KROIA/Voicemail-Box/Software/BSP_VoiceMailBox/documentation/MP3_decoder.md

# MP3_decoder
The MP3 decoder library used in this project is from the [X-CUBE-AUDIO](https://www.st.com/en/embedded-software/x-cube-audio.html) example project.
The MP3_decoder class is just a C++ wrapper to make it easy to use the library.
The decoder is used to read mp3 encoded data from a source like a file and decode it back to audio samples that can then passed to the I2S TX DMA buffer, providing the speaker with sound.
You can find a ready to run project [here](../../Demos/F469/F469_MultiExample/README.md).

---
## Content
- [Features](#features)
- [Setup](#setup)
- [Usage](#usage)

---
## Features
- Decodes mp3 data live to analog samples

---
## Setup
- Uses the Spirit MP3 library for encoding and decoding. [Click here](../../Demos/F469/F469_HelloAudio/README.md/#spiritdsp-mp3) to learn how to include the library.
- Place a mp3 file with the name `music.mp3` onto the SD-Card.
- Make sure the C++ application is setup in order to use this class
You can find the instructions on how to do so [here](CppFromC.md).

---
## Usage
This example takes a `music.mp3` file and converts it to a `conv.wav` file.
``` C++ 
// Application.cpp
#include "BSP_VoiceMailBox.hpp" // includes "peripherals/i2s.hpp"

unsigned int decoderReadCallback(
        void* pMP3_decoderCompressedData,
        unsigned int nMP3_decoderDataSizeInChars,
        void* pUserData);

VoiceMailBox::WAVFile* wavFile = nullptr;
VoiceMailBox::File* mp3File = nullptr;
VoiceMailBox::MP3_decoder* decoder = nullptr;

void setup()
{
    // decoderReadCallback: function that gets called by the MP3_decoder to read compressed data from the MP3 file.
    // &mp3File: pointer to the MP3 file that is being read. (any void* can be used here, but we use a pointer to the MP3 file for convenience)
    // 4: samplesize in bytes. [int16_t(LEFT), int16_t(RIGHT)] is one sample
    decoder = new VoiceMailBox::MP3_decoder(decoderReadCallback, mp3File, 4);

    mp3File = new VoiceMailBox::File();
    wavFile = new VoiceMailBox::WAVFile();
    wavFile->setSampleRate(48000); // Set sample rate to 48kHz
    wavFile->setNumChannels(2);    // Stereo recording
    wavFile->setBitsPerSample(16); // Set bits per sample to 16

    if (!mp3File->open("music.mp3", VoiceMailBox::File::AccessMode::read))
    {
        VoiceMailBox::println("Failed to open file for reading.");
    }
    if (!wavFile->open("conv.wav", VoiceMailBox::File::AccessMode::write))
    {
        VoiceMailBox::println("Failed to open file for writing.");
    }
}

void loop()
{
    static bool finished = false;
    if (finished)
        return;
    if (!mp3File->isOpen())
    {
        VoiceMailBox::println("mp3File is not open");
        VoiceMailBox::delay(1000);
        return;
    }
    if (!wavFile->isOpen())
    {
        VoiceMailBox::println("wavFile is not open");
        VoiceMailBox::delay(1000);
        return;
    }

    const size_t sampleCount = 576; // Number of samples per frame for MP3 (2 channels, 16 bits per sample)
    int16_t data[sampleCount*2] = { 0 }; // Buffer to hold decoded audio samples
    VoiceMailBox::println("Starting MP3 decoding...");
    while (!mp3File->eof())
    {
        // Request <sampleCount> samples from the MP3 decoder
        unsigned int samplesRead = decoder->decode(data, sampleCount);
        static bool firstRun = true;
        if (firstRun)
        {
            samplesRead = decoder->decode(data, sampleCount); // For the first run, the decoding must be done twice to prevent noise
            firstRun = false;
        }
        if (samplesRead == 0)
        {
            // End of file
            break;
        }

        // Write the decoded audio data to the WAV file
        wavFile->writeAudioSamples(data, samplesRead); // 4 bytes per sample (2 channels * 2 bytes per channel)
    }
    VoiceMailBox::println("Decoding finished");
    mp3File->close();
    wavFile->close();
    finished = true;
}

// This function is called by the MP3_decoder to read compressed data from the MP3 file.
unsigned int decoderReadCallback(
    void* pMP3_decoderCompressedData,
    unsigned int nMP3_decoderDataSizeInChars,
    void* pUserData)
{
    // The pUserData is the pointer that was passed by the MP3_decoder constructor, which is a pointer to the mp3File->
    VoiceMailBox::File* file = (VoiceMailBox::File*)pUserData;
    if (file->isOpen())
    {
        // Read the MP3_decoder data from the file
        uint32_t bytesRead = file->read((uint8_t*)pMP3_decoderCompressedData, nMP3_decoderDataSizeInChars);
        return bytesRead;
    }
    return 0;
}
```
