KROIA/Voicemail-Box/Hardware/Diagramms/Blockschaltbild KW9.pdf

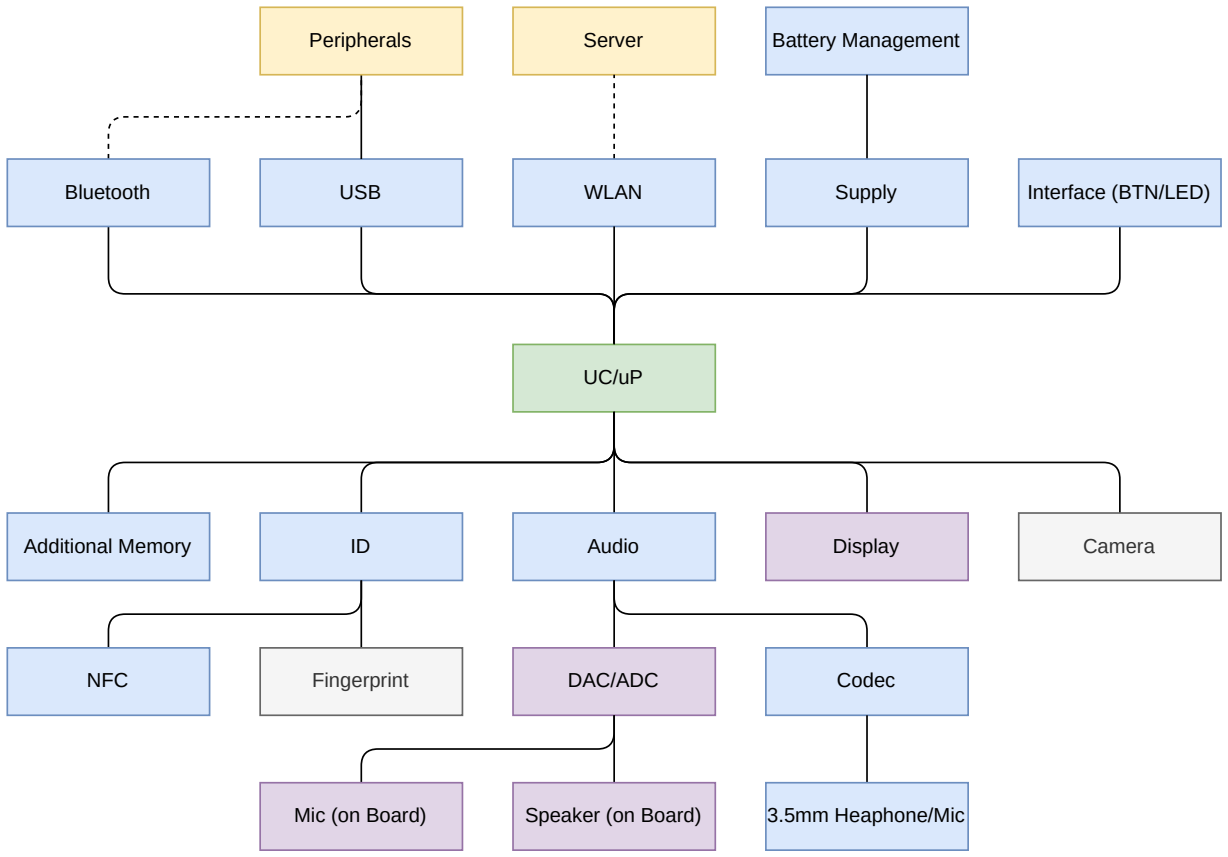
[picture p33: figure]
Bluetooth; USB; Peripherals; Server; WLAN; Battery Management; Supply; NFC; Fingerprint; Audio; DAC/ADC; Codec; Mic (on Board); Speaker (on Board); 3.5mm Heaphone/Mic; Display; Camera; Interface (BTN/LED); Additional Memory

Processor Source
Parts HW required
Parts HW Wish
Parts HW rejected
Parts external

Case
(3D Print)

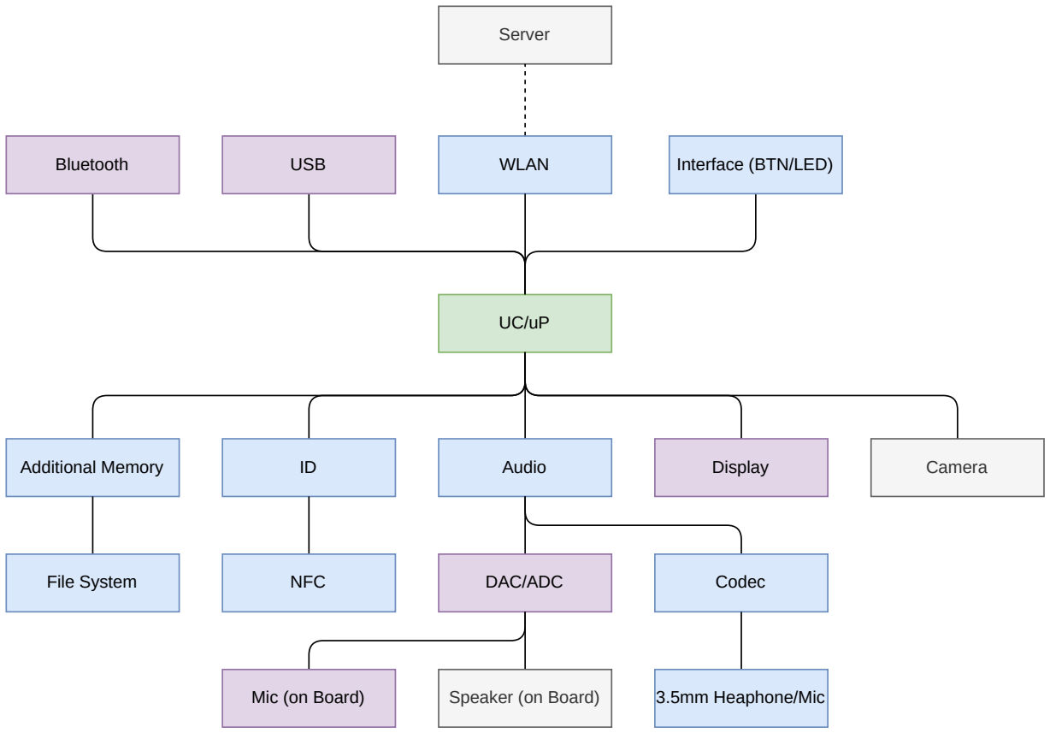
[picture p34: figure]
Bluetooth; USB; Server; WLAN; NFC; Audio; DAC/ADC; Codec; Mic (on Board); Speaker (on Board); 3.5mm Heaphone/Mic; Display; Camera; Interface (BTN/LED); Additional Memory; File System

Processor Source
SW required
SW Wish
SW if too much time
