KROIA/Voicemail-Box/Hardware/Picture/20250507_130045.jpg

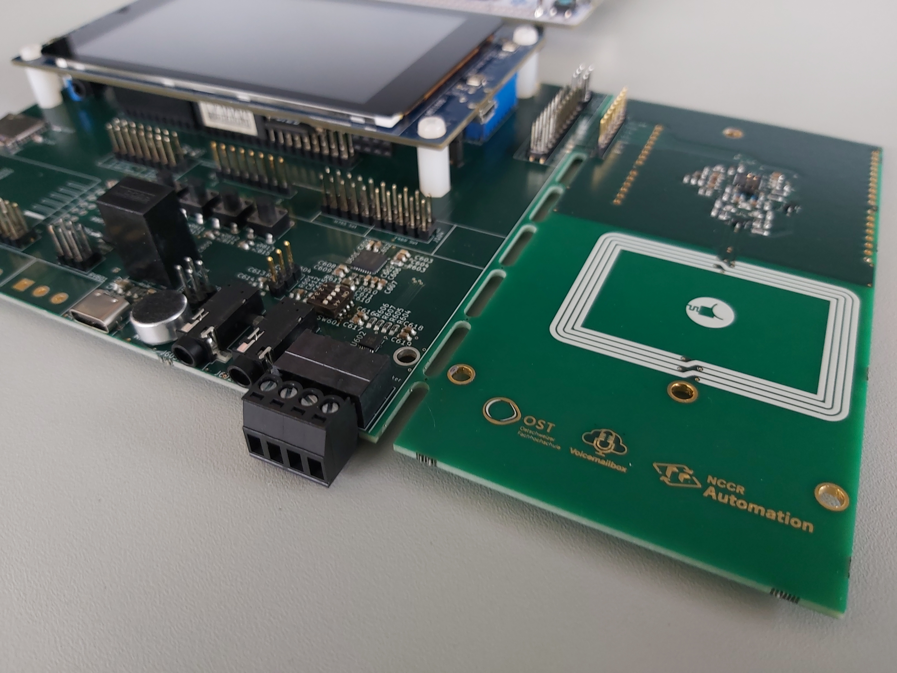
Hardware/Picture/20250507_130045.jpg
