KROIA/Voicemail-Box/Hardware/Picture/20250507_130126.jpg

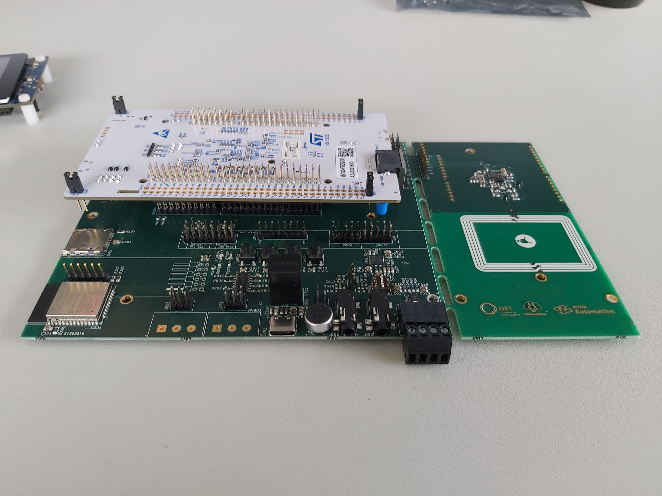
Hardware/Picture/20250507_130126.jpg
