KROIA/Voicemail-Box/Software/DevSandbox/Audio/Opus_bitrate+latency_comparison.svg.png

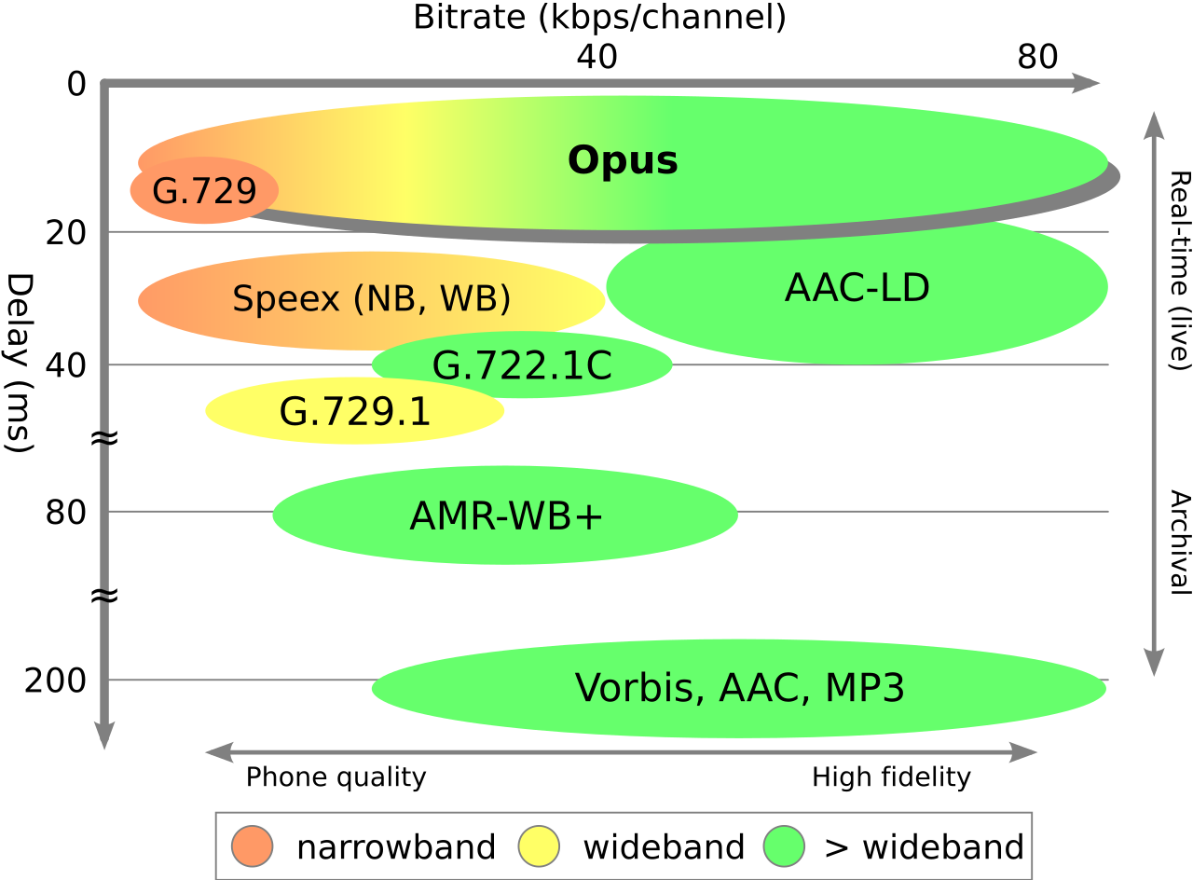
Software/DevSandbox/Audio/Opus_bitrate+latency_comparison.svg.png
