KROIA/Voicemail-Box/Software/BSP_VoiceMailBox/src/peripherals/Codec_TLV320AIC3104.cpp

#include "peripherals/Codec_TLV320AIC3104.hpp"
#include "platform.hpp"

namespace VoiceMailBox
{
	Codec_TLV320AIC3104::Codec_TLV320AIC3104(VMB_I2S_Handle* i2sHandle, uint16_t i2sBufferSize,
											 I2C& i2c, uint8_t i2cDeviceAddress,
											 VMB_GPIO* resetPort, uint16_t resetPin, bool resetPinIsInverted)
		: AudioCodec()
#ifdef VMB_USE_LOGGER_OBJECTS
		, Logger("Codec_TLV320AIC3104")
#endif
		, m_i2c(i2c)
		, m_i2cDeviceAddress(i2cDeviceAddress)
		, m_resetPin{ resetPort, resetPin, resetPinIsInverted }
		, m_i2s(i2sHandle, i2sBufferSize)
		, m_currentRegisterPage(0)
	{
#if defined(VMB_ENABLE_CODEC_PERFORMANCE_MEASUREMENTS)
		m_i2s.setHalfCpltCallback([this](I2S& caller) { onI2S_DMA_TxRx_HalfCpltCallback(); });
		m_i2s.setCpltCallback([this](I2S& caller) { onI2S_DMA_TxRx_CpltCallback(); });
#endif
	}

	Codec_TLV320AIC3104::~Codec_TLV320AIC3104()
	{

	}

	void Codec_TLV320AIC3104::reset()
	{
		m_resetPin.set(true); 
		VMB_HAL_Delay(25); // Wait for 10ms
		m_resetPin.set(false); 
		VMB_HAL_Delay(25); // Wait for 10ms

		// Software reset
		writeRegister(REG::PAGE_0::SOFTWRE_RESET, 0x01); // Example register write for software reset
		VMB_HAL_Delay(10); // Wait for 10ms
	}
	bool Codec_TLV320AIC3104::setup()
	{
		bool success = true;
		reset(); // Reset the codec
		setCurrentRegisterPage(0); // Set the current register page to 0

		// Initialize codec registers
		success &= writeRegister(REG::PAGE_0::PLL_PROGRAMMING_A, 0x10); //Disable PLL, 2 = 4. MCLK = 256 * 48Khz, fs(ref) = MCLK / (128 * Q)


		float gainDB = 0;
		uint32_t microphoneGainDB_2 = (uint32_t)(2.f * gainDB) & 0xEF;
		success &= writeRegister(REG::PAGE_0::LEFT_ADC_PGA_GAIN_CONTROL,  0x00 | microphoneGainDB_2); //Un-mute left ADC PGA
		success &= writeRegister(REG::PAGE_0::RIGHT_ADC_PGA_GAIN_CONTROL, 0x00 | microphoneGainDB_2); //Un-mute right ADC PGA
		success &= writeRegister(REG::PAGE_0::MIC2_L_R_TO_LEFT_ADC_CONTROL, 0x0F); //Connect MIC2L/LINE2L to left ADC PGA (@0db gain), do not connect MIC2R/LINE2R to left ADC PGA
		success &= writeRegister(REG::PAGE_0::MIC2_LINE2_TO_RIGHT_ADC_CONTROL, 0xF0); //Connect MIC2R/LINE2R to right ADC PGA (@0db gain), do not connect MIC2L/LINE2L to right ADC PGA
		success &= writeRegister(REG::PAGE_0::MIC1LP_LINE1LP_TO_LEFT_ADC_CONTROL, 0x7C); //Power up left ADC
		success &= writeRegister(REG::PAGE_0::MIC1RP_LINE1RP_TO_RIGHT_ADC_CONTROL, 0x7C); //Power up right ADC


		success &= writeRegister(REG::PAGE_0::CODEC_DATA_PATH_SETUP, 0x0A); //fs(ref) = 48khz, left DAC data path plays left-channel input data, right DAC -> right-channel input data

		
		

		success &= writeRegister(REG::PAGE_0::AUDIO_SERIAL_DATA_INTERFACE_CONTROL_B, 0x07); // Enable Re-Sync for ADC and DAC

		success &= writeRegister(REG::PAGE_0::AUDIO_CODEC_DIGITAL_FILTER_CONTROL, 0x00); // Bypass digital filter
		success &= writeRegister(REG::PAGE_0::AUDIO_SERIAL_DATA_INTERFACE_CONTROL_A, 0x00); // Disable 3D effect and others
		

		success &= writeRegister(REG::PAGE_0::DAC_OUTPUT_SWITCHING_CONTROL, 0xA0); // Set Output-switch of DAC_L -> DAC_L2, DAC_R -> DAC_R2


		success &= writeRegister(REG::PAGE_0::DAC_L1_TO_HPLOUT_VOLUME_CONTROL, 0x00); // Disconnect DAC_L1 from HPLOUT
		success &= writeRegister(REG::PAGE_0::DAC_R1_TO_HPLOUT_VOLUME_CONTROL, 0x00); // Disconnect DAC_R1 from HPLOUT
		success &= writeRegister(REG::PAGE_0::PGA_L_TO_HPLOUT_VOLUME_CONTROL, 0x00); // Disconnect PGA_L from HPLOUT
		success &= writeRegister(REG::PAGE_0::PGA_R_TO_HPLOUT_VOLUME_CONTROL, 0x00); // Disconnect PGA_R from HPLOUT

		success &= writeRegister(REG::PAGE_0::DAC_L1_TO_HPROUT_VOLUME_CONTROL, 0x00); // Disconnect DAC_L1 from HPROUT
		success &= writeRegister(REG::PAGE_0::DAC_R1_TO_HPROUT_VOLUME_CONTROL, 0x00); // Disconnect DAC_R1 from HPROUT
		success &= writeRegister(REG::PAGE_0::PGA_L_TO_HPROUT_VOLUME_CONTROL, 0x00); // Disconnect PGA_L from HPROUT
		success &= writeRegister(REG::PAGE_0::PGA_R_TO_HPROUT_VOLUME_CONTROL, 0x00); // Disconnect PGA_R from HPROUT

		

		success &= writeRegister(REG::PAGE_0::LEFT_DAC_DIGITAL_VOLUME_CONTROL, 0x00); //Unmute left DAC channel
		success &= writeRegister(REG::PAGE_0::RIGHT_DAC_DIGITAL_VOLUME_CONTROL, 0x00); //Unmute right DAC channel
		success &= writeRegister(REG::PAGE_0::HPLOUT_OUTPUT_LEVEL_CONTROL, 0x0B); //Unmute left line output (HPLOUT) @ 0dB gain
		success &= writeRegister(REG::PAGE_0::HPROUT_OUTPUT_LEVEL_CONTROL, 0x0B); //Unmute right line output (HPROUT) @ 0dB gain


		success &= writeRegister(REG::PAGE_0::ADC_POWER_AND_OUTPUT_DRIVER_CONTROL, 0xA0); //Power up left and right DAC



		//writeRegister(REG::PAGE_0::HIGH_POWER_OUTPUT_STAGE_CONTROL, 0x80); //Output common mode voltage = 1,65V (= VCC / 2)
		
		//writeRegister(REG::PAGE_0::DAC_L1_TO_LEFT_LOP_M_VOLUME_CONTROL, 0x80); //Route left DAC to left line output
		//writeRegister(REG::PAGE_0::LEFT_LOP_M_OUTPUT_LEVEL_CONTROL, 0x0B); //Unmute left line output
		success &= writeRegister(REG::PAGE_0::CLOCK, 0x01); //CODEC_CLKIN uses CLKDIV_OUT

		// Setup I2S for DMA transmit and receive
		if (!m_i2s.startDMA())
		{
			VMB_LOGLN("Failed to start I2S DMA");
			success = false;
		}
		if (!success)
		{
			VMB_LOGLN("Codec_TLV320AIC3104 setup failed");
		}
		return success;
	}

	void Codec_TLV320AIC3104::onI2S_DMA_TxRx_HalfCpltCallback()
	{
		// Inside ISR context! 
#ifdef VMB_ENABLE_CODEC_PERFORMANCE_MEASUREMENTS
		m_DMA_halfTransferTick = VMB_HAL_GetTickCountInMs();
#endif
#if  defined(VMB_DEVELOPMENT_ENABLE_DBG_PINS_IN_CODEC) && defined(VMB_USE_INTERNAL_LEDS)
		Platform::getDebugPin(DBG_PIN::DBG0).set(1); // Set DBG0 on
#endif
	}
	void Codec_TLV320AIC3104::onI2S_DMA_TxRx_CpltCallback()
	{
		// Inside ISR context! 
#ifdef VMB_ENABLE_CODEC_PERFORMANCE_MEASUREMENTS
		m_DMA_halfProcessingTicks = VMB_HAL_GetTickCountInMs() - m_DMA_halfTransferTick;
#endif
#if defined(VMB_DEVELOPMENT_ENABLE_DBG_PINS_IN_CODEC) && defined(VMB_USE_INTERNAL_LEDS)
		Platform::getDebugPin(DBG_PIN::DBG0).set(0); // Set DBG0 off
#endif
	}


	void Codec_TLV320AIC3104::startDataProcessing()
	{
#ifdef VMB_ENABLE_CODEC_PERFORMANCE_MEASUREMENTS
		m_startDataProcessingTick = VMB_HAL_GetTickCountInMs();
#endif
	}
	void Codec_TLV320AIC3104::endDataProcessing()
	{
#ifdef VMB_ENABLE_CODEC_PERFORMANCE_MEASUREMENTS
		m_dataProcessingTicks = VMB_HAL_GetTickCountInMs() - m_startDataProcessingTick;
#endif
	}

	void Codec_TLV320AIC3104::setMicrophoneGainDB(float db)
	{
		uint8_t leftGainReg = readRegister(REG::PAGE_0::LEFT_ADC_PGA_GAIN_CONTROL);
		uint8_t rightGainReg = readRegister(REG::PAGE_0::RIGHT_ADC_PGA_GAIN_CONTROL);

		if(db < 0)
			db = 0;
		else if (db > 59.5)
			db = 59.5;
		uint32_t microphoneGainDB_2 = (uint32_t)(2.f * db) & 0xEF;
		leftGainReg  = (leftGainReg & 0x01)  | microphoneGainDB_2;
		rightGainReg = (rightGainReg & 0x01) | microphoneGainDB_2;

		writeRegister(REG::PAGE_0::LEFT_ADC_PGA_GAIN_CONTROL, leftGainReg); //Un-mute left ADC PGA
		writeRegister(REG::PAGE_0::RIGHT_ADC_PGA_GAIN_CONTROL, rightGainReg); //Un-mute right ADC PGA
	}

	bool Codec_TLV320AIC3104::writeRegister(uint8_t registerAddress, uint8_t data)
	{
		VMB_HAL_Status status = m_i2c.writeRegister(m_i2cDeviceAddress, registerAddress, data);
		VMB_LOGGER_LOG_STATUS(status, "Codec_TLV320AIC3104::writeRegister("+std::to_string(registerAddress)+","+std::to_string(data)+")");
		return status == VMB_HAL_Status::OK;
	}

	uint8_t Codec_TLV320AIC3104::readRegister(uint8_t registerAddress)
	{
		uint8_t data = 0;
		VMB_HAL_Status status = m_i2c.readRegister(m_i2cDeviceAddress, registerAddress, data);
		VMB_LOGGER_LOG_STATUS(status, "Codec_TLV320AIC3104::readRegister("+std::to_string(registerAddress)+")");
		return data;
	}

	uint8_t Codec_TLV320AIC3104::getCurrentRegisterPage()
	{
		return readRegister(REG::PAGE_0::PAGE_SELECT); // Read the current register page
	}
	void Codec_TLV320AIC3104::setCurrentRegisterPage(uint8_t page)
	{
		writeRegister(REG::PAGE_0::PAGE_SELECT, page & 0x01); // Set the current register page
		m_currentRegisterPage = page & 0x01; // Update the current register page

		// Readback the current register page to verify
		uint8_t currentPage = getCurrentRegisterPage();
		if (currentPage != m_currentRegisterPage)
		{
			// Handle error
			VMB_LOGLN("Failed to set register page to " + std::to_string(page) + ", current page is " + std::to_string(currentPage));
		}
	}


	
}
