KROIA/Voicemail-Box/Software/Demos/F469/F469_HelloAudio/Core/Src/main.c

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
/* Includes ------------------------------------------------------------------*/
#include "main.h"
#include "fatfs.h"
#include "usb_host.h"

/* USER CODE BEGIN Includes */
#include "Application.h"
/* USER CODE END Includes */

ADC_HandleTypeDef hadc1;
ADC_HandleTypeDef hadc2;

CRC_HandleTypeDef hcrc;

DMA2D_HandleTypeDef hdma2d;

DSI_HandleTypeDef hdsi;

I2C_HandleTypeDef hi2c1;
I2C_HandleTypeDef hi2c2;

I2S_HandleTypeDef hi2s2;
DMA_HandleTypeDef hdma_i2s2_ext_rx;
DMA_HandleTypeDef hdma_spi2_tx;

LTDC_HandleTypeDef hltdc;

SD_HandleTypeDef hsd;
DMA_HandleTypeDef hdma_sdio_rx;
DMA_HandleTypeDef hdma_sdio_tx;

TIM_HandleTypeDef htim1;

UART_HandleTypeDef huart3;
UART_HandleTypeDef huart6;

SDRAM_HandleTypeDef hsdram1;

/* USER CODE BEGIN PV */
ADC_HandleTypeDef* getADC_POT0()
{
	return &hadc1;
}
ADC_HandleTypeDef* getADC_POT1()
{
	return &hadc2;
}
UART_HandleTypeDef* getUART_DEBUG()
{
	return &huart3;
}
UART_HandleTypeDef* getUART_WIFI()
{
	return &huart6;
}
I2C_HandleTypeDef* getI2C_Handle()
{
	return &hi2c1;
}
I2S_HandleTypeDef* getI2S_CODEC()
{
	return &hi2s2;
}
/* USER CODE END PV */

void SystemClock_Config(void);
void PeriphCommonClock_Config(void);
static void MX_GPIO_Init(void);
static void MX_DMA_Init(void);
static void MX_CRC_Init(void);
static void MX_DMA2D_Init(void);
static void MX_DSIHOST_DSI_Init(void);
static void MX_FMC_Init(void);
static void MX_I2C1_Init(void);
static void MX_I2C2_Init(void);
static void MX_LTDC_Init(void);
static void MX_SDIO_SD_Init(void);
static void MX_TIM1_Init(void);
static void MX_USART3_UART_Init(void);
static void MX_USART6_UART_Init(void);
static void MX_ADC1_Init(void);
static void MX_ADC2_Init(void);
static void MX_I2S2_Init(void);
void MX_USB_HOST_Process(void);

/**
  * @brief  The application entry point.
  * @retval int
  */
int main(void)
{

  /* MCU Configuration--------------------------------------------------------*/

  /* Reset of all peripherals, Initializes the Flash interface and the Systick. */
  HAL_Init();

  /* Configure the system clock */
  SystemClock_Config();

  /* Configure the peripherals common clocks */
  PeriphCommonClock_Config();

  /* Initialize all configured peripherals */
  MX_GPIO_Init();
  MX_DMA_Init();
  MX_CRC_Init();
  MX_DMA2D_Init();
  MX_DSIHOST_DSI_Init();
  MX_FMC_Init();
  MX_I2C1_Init();
  MX_I2C2_Init();
  MX_LTDC_Init();
  MX_SDIO_SD_Init();
  MX_TIM1_Init();
  MX_USART3_UART_Init();
  MX_USART6_UART_Init();
  MX_FATFS_Init();
  MX_USB_HOST_Init();
  MX_ADC1_Init();
  MX_ADC2_Init();
  MX_I2S2_Init();
  /* USER CODE BEGIN 2 */
  setup(); // Calls the setup function from the Application.h
  /* USER CODE END 2 */

  /* Infinite loop */
  /* USER CODE BEGIN WHILE */
  while (1)
  {
	loop(); // Calls the loop function from the Application.h
    /* USER CODE END WHILE */
    MX_USB_HOST_Process();

    /* USER CODE BEGIN 3 */
  }
  /* USER CODE END 3 */
}

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
/**
  * @brief  Period elapsed callback in non blocking mode
  * @note   This function is called  when TIM6 interrupt took place, inside
  * HAL_TIM_IRQHandler(). It makes a direct call to HAL_IncTick() to increment
  * a global variable "uwTick" used as application time base.
  * @param  htim : TIM handle
  * @retval None
  */
void HAL_TIM_PeriodElapsedCallback(TIM_HandleTypeDef *htim)
{
  if (htim->Instance == TIM6) {
    HAL_IncTick();
  }
}

/**
  * @brief  This function is executed in case of error occurrence.
  * @retval None
  */
void Error_Handler(void)
{
  /* USER CODE BEGIN Error_Handler_Debug */
  /* User can add his own implementation to report the HAL error return state */
  __disable_irq();
  while (1)
  {
  }
  /* USER CODE END Error_Handler_Debug */
}

#ifdef  USE_FULL_ASSERT
/**
  * @brief  Reports the name of the source file and the source line number
  *         where the assert_param error has occurred.
  * @param  file: pointer to the source file name
  * @param  line: assert_param error line source number
  * @retval None
  */
void assert_failed(uint8_t *file, uint32_t line)
{
  /* USER CODE BEGIN 6 */
  /* User can add his own implementation to report the file name and line number,
     ex: printf("Wrong parameters value: file %s on line %d\r\n", file, line) */
  /* USER CODE END 6 */
}
#endif /* USE_FULL_ASSERT */
