KROIA/Voicemail-Box/Software/Demos/H755/H755_HelloAudio/CM7/Core/Src/main.c

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
/* Includes ------------------------------------------------------------------*/
#include "main.h"
#include "fatfs.h"

/* USER CODE BEGIN Includes */
#include "Application.h"
/* USER CODE END Includes */

/* USER CODE BEGIN PD */

#ifndef HSEM_ID_0
#define HSEM_ID_0 (0U) /* HW semaphore 0*/
#endif

/* USER CODE END PD */

ADC_HandleTypeDef hadc1;
ADC_HandleTypeDef hadc3;

I2C_HandleTypeDef hi2c1;

I2S_HandleTypeDef hi2s2;

SD_HandleTypeDef hsd1;

UART_HandleTypeDef huart1;
UART_HandleTypeDef huart3;

/* USER CODE BEGIN PV */
ADC_HandleTypeDef* getADC_POT0()
{
	return &hadc1;
}
ADC_HandleTypeDef* getADC_POT1()
{
	return &hadc3;
}
UART_HandleTypeDef* getUART_DEBUG()
{
	return &huart3;
}
UART_HandleTypeDef* getUART_WIFI()
{
	return &huart1;
}
I2C_HandleTypeDef* getI2C_Handle()
{
	return &hi2c1;
}
I2S_HandleTypeDef* getI2S_CODEC()
{
	return &hi2s2;
}
/* USER CODE END PV */

void SystemClock_Config(void);
void PeriphCommonClock_Config(void);
static void MX_GPIO_Init(void);
static void MX_ADC1_Init(void);
static void MX_ADC3_Init(void);
static void MX_USART1_UART_Init(void);
static void MX_USART3_UART_Init(void);
static void MX_I2C1_Init(void);
static void MX_SDMMC1_SD_Init(void);
static void MX_I2S2_Init(void);
/**
  * @brief  The application entry point.
  * @retval int
  */
int main(void)
{

/* USER CODE BEGIN Boot_Mode_Sequence_0 */
  int32_t timeout;
/* USER CODE END Boot_Mode_Sequence_0 */

/* USER CODE BEGIN Boot_Mode_Sequence_1 */
  /* Wait until CPU2 boots and enters in stop mode or timeout*/
  timeout = 0xFFFF;
  while((__HAL_RCC_GET_FLAG(RCC_FLAG_D2CKRDY) != RESET) && (timeout-- > 0));
  if ( timeout < 0 )
  {
  Error_Handler();
  }
/* USER CODE END Boot_Mode_Sequence_1 */
  /* MCU Configuration--------------------------------------------------------*/

  /* Reset of all peripherals, Initializes the Flash interface and the Systick. */
  HAL_Init();

  /* Configure the system clock */
  SystemClock_Config();

  /* Configure the peripherals common clocks */
  PeriphCommonClock_Config();
/* USER CODE BEGIN Boot_Mode_Sequence_2 */
/* When system initialization is finished, Cortex-M7 will release Cortex-M4 by means of
HSEM notification */
/*HW semaphore Clock enable*/
__HAL_RCC_HSEM_CLK_ENABLE();
/*Take HSEM */
HAL_HSEM_FastTake(HSEM_ID_0);
/*Release HSEM in order to notify the CPU2(CM4)*/
HAL_HSEM_Release(HSEM_ID_0,0);
/* wait until CPU2 wakes up from stop mode */
timeout = 0xFFFF;
while((__HAL_RCC_GET_FLAG(RCC_FLAG_D2CKRDY) == RESET) && (timeout-- > 0));
if ( timeout < 0 )
{
Error_Handler();
}
/* USER CODE END Boot_Mode_Sequence_2 */

  /* Initialize all configured peripherals */
  MX_GPIO_Init();
  MX_ADC1_Init();
  MX_ADC3_Init();
  MX_USART1_UART_Init();
  MX_USART3_UART_Init();
  MX_I2C1_Init();
  MX_FATFS_Init();
  MX_SDMMC1_SD_Init();
  MX_I2S2_Init();
  /* Infinite loop */
  /* USER CODE BEGIN WHILE */
  setup();
  while (1)
  {

	  loop();
    /* USER CODE END WHILE */

    /* USER CODE BEGIN 3 */
  }
  /* USER CODE END 3 */
}

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
