KROIA/Voicemail-Box/Software/DevSandbox/NFC/NFC_Demo/CM7/Core/Inc/custom_bus.h

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

/* Define to prevent recursive inclusion -------------------------------------*/
#ifndef CUSTOM_BUS_H
#define CUSTOM_BUS_H

#ifdef __cplusplus
 extern "C" {
#endif

/* Includes ------------------------------------------------------------------*/
#include "custom_conf.h"
#include "custom_errno.h"

/** @addtogroup BSP
  * @{
  */

/** @addtogroup CUSTOM
  * @{
  */

/** @defgroup CUSTOM_BUS CUSTOM BUS
  * @{
  */

/** @defgroup CUSTOM_BUS_Exported_Constants CUSTOM BUS Exported Constants
  * @{
  */

#define BUS_SPI1_INSTANCE SPI1
#define BUS_SPI1_SCK_GPIO_CLK_DISABLE() __HAL_RCC_GPIOA_CLK_DISABLE()
#define BUS_SPI1_SCK_GPIO_PORT GPIOA
#define BUS_SPI1_SCK_GPIO_PIN GPIO_PIN_5
#define BUS_SPI1_SCK_GPIO_AF GPIO_AF5_SPI1
#define BUS_SPI1_SCK_GPIO_CLK_ENABLE() __HAL_RCC_GPIOA_CLK_ENABLE()
#define BUS_SPI1_MISO_GPIO_PIN GPIO_PIN_6
#define BUS_SPI1_MISO_GPIO_PORT GPIOA
#define BUS_SPI1_MISO_GPIO_CLK_DISABLE() __HAL_RCC_GPIOA_CLK_DISABLE()
#define BUS_SPI1_MISO_GPIO_CLK_ENABLE() __HAL_RCC_GPIOA_CLK_ENABLE()
#define BUS_SPI1_MISO_GPIO_AF GPIO_AF5_SPI1
#define BUS_SPI1_MOSI_GPIO_CLK_ENABLE() __HAL_RCC_GPIOB_CLK_ENABLE()
#define BUS_SPI1_MOSI_GPIO_PORT GPIOB
#define BUS_SPI1_MOSI_GPIO_PIN GPIO_PIN_5
#define BUS_SPI1_MOSI_GPIO_CLK_DISABLE() __HAL_RCC_GPIOB_CLK_DISABLE()
#define BUS_SPI1_MOSI_GPIO_AF GPIO_AF5_SPI1

#ifndef BUS_SPI1_POLL_TIMEOUT
  #define BUS_SPI1_POLL_TIMEOUT                   0x1000U
#endif
/* SPI1 Baud rate in bps  */
#ifndef BUS_SPI1_BAUDRATE
   #define BUS_SPI1_BAUDRATE   10000000U /* baud rate of SPIn = 10 Mbps*/
#endif

/**
  * @}
  */

/** @defgroup CUSTOM_BUS_Private_Types CUSTOM BUS Private types
  * @{
  */
#if (USE_HAL_SPI_REGISTER_CALLBACKS == 1U)
typedef struct
{
  pSPI_CallbackTypeDef  pMspInitCb;
  pSPI_CallbackTypeDef  pMspDeInitCb;
}BSP_SPI_Cb_t;
#endif /* (USE_HAL_SPI_REGISTER_CALLBACKS == 1U) */
/**
  * @}
  */

/** @defgroup CUSTOM_LOW_LEVEL_Exported_Variables LOW LEVEL Exported Constants
  * @{
  */

extern SPI_HandleTypeDef hspi1;

/**
  * @}
  */

/** @addtogroup CUSTOM_BUS_Exported_Functions
  * @{
  */

/* BUS IO driver over SPI Peripheral */
HAL_StatusTypeDef MX_SPI1_Init(SPI_HandleTypeDef* hspi);
int32_t BSP_SPI1_Init(void);
int32_t BSP_SPI1_DeInit(void);
int32_t BSP_SPI1_Send(uint8_t *pData, uint16_t Length);
int32_t BSP_SPI1_Recv(uint8_t *pData, uint16_t Length);
int32_t BSP_SPI1_SendRecv(uint8_t *pTxData, uint8_t *pRxData, uint16_t Length);
#if (USE_HAL_SPI_REGISTER_CALLBACKS == 1U)
int32_t BSP_SPI1_RegisterDefaultMspCallbacks (void);
int32_t BSP_SPI1_RegisterMspCallbacks (BSP_SPI_Cb_t *Callbacks);
#endif /* (USE_HAL_SPI_REGISTER_CALLBACKS == 1U) */

int32_t BSP_GetTick(void);

/**
  * @}
  */

/**
  * @}
  */

/**
  * @}
  */

/**
  * @}
  */
#ifdef __cplusplus
}
#endif

#endif /* CUSTOM_BUS_H */
