KROIA/Voicemail-Box/Software/BSP_VoiceMailBox/src/utilities/Updatable.cpp

#include "utilities/Updatable.hpp"
#include <algorithm>

namespace VoiceMailBox
{


	Updatable::Updatable()
	{
		getInstances().push_back(this);
	}
	Updatable::~Updatable()
	{
		std::vector<Updatable*> &updatable = getInstances();
		auto it = std::find(updatable.begin(), updatable.end(), this);
		if (it != updatable.end())
			updatable.erase(it);
	}

	void Updatable::updateInstances()
	{
		const std::vector<Updatable*> &objs = getInstances();
		size_t size = objs.size();
		for (size_t i=0; i<size; ++i)
			objs[i]->update();
	}

	std::vector<Updatable*> &Updatable::getInstances()
	{
		static std::vector<Updatable*> updatables;
		return updatables;
	}

}
