KROIA/Voicemail-Box/Software/Demos/F469/F469_MultiExample/Application/inc/Application.h

#ifndef APPLICATION_H
#define APPLICATION_H

#ifdef __cplusplus
extern "C" {
#endif

// C functions, callable from c and c++ code
extern void setup();
extern void loop();

#ifdef __cplusplus
}
#endif
#endif /* APPLICATION_H */
